fattiebunnie/keyboard/resources/documentations/201808291634499387800.jpg

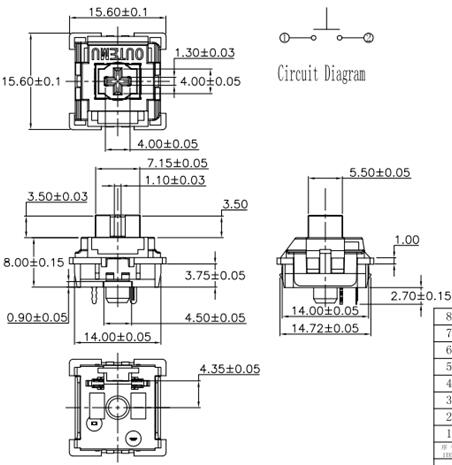
resources/documentations/201808291634499387800.jpg
